SebastianOberschwendtner/OTP22_oScale/01_Code/src/gui.c

/**
 * OTP-22 oScale Firmware
 * Copyright (c) 2020 Sebastian Oberschwendtner, sebastian.oberschwendtner@gmail.com
 *
 *
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
 */
/**
 ******************************************************************************
 * @file    gui.c
 * @author  SO
 * @version V1.0.0
 * @date    22-November-2020
 * @brief   The GUI of the oScale.
 ******************************************************************************
 */
// ****** Includes ******
#include "gui.h"

// ****** Variables ******
task_t taskGUI; // Task struct for GUI
char buffer1[16]; // Buffer1 for display string
char buffer2[16]; // Buffer2 for display string
/*
 => double buffering is used, because the GUI does not know when the display is finished
 sending the data. Otherwise the GUI would override the content of the buffer while it
 is sent.
 */
ScaleDat_t* datGUI;  // Pointer to the system data.

// ****** Functions ******

/**
 **********************************************************
 * @brief TASK GUI
 **********************************************************
 * The GUI task.
 * 
 **********************************************************
 * @details
 * @Execution:	Non-interruptable
 **********************************************************
 */
void Task_GUI(void)
{
    // Switch for active command
    switch (taskGUI.command)
    {
    case GUI_CMD_INIT:
        gui_Init();
        break;

    case GUI_CMD_MANUAL:
        gui_DisplayManual();
        break;

    default:
        break;
    }
};

/**
 * @brief Initialize the GUI Data.
 */
void gui_InitTask(void)
{
    sarb_InitStruct(&taskGUI);
    taskGUI.command = GUI_CMD_INIT;

    // Get the pointer to the system data
    datGUI = Scale_GetIPC();
};

/**
 * @brief Initialize the GUI interface.
 */
void gui_Init(void)
{
    // Perform the command sequences
    switch (taskGUI.sequence)
    {
        case 0:
            // Write the header line
            if (gui_WriteString(0, 0, strcpy(buffer1, "oScale")))
                taskGUI.sequence++;
            break;

        case 1:
            // Write version to the header line
            if (gui_WriteString(8, 0, strcpy(buffer2, VERSION)))
                taskGUI.sequence++;
            break;

        case 2:
            // Write the horizontal line
            if (disp_CallByValue(DISP_CMD_LINE_H, 0, 128, 8))
                taskGUI.sequence++;
            break;

        case 3:
            taskGUI.counter = 0;
            // Write the vertical line
            if (disp_CallByValue(DISP_CMD_LINE_V, 1, 7, 64))
                taskGUI.sequence++;
            break;

        case 4:
            // Write the weight descriptor
            if (gui_WriteString(0, 2, strcpy(buffer1, "Weight")))
                taskGUI.sequence++;
            break;

        case 5:
            // Write the Time descriptor
            if (gui_WriteString(11, 2, strcpy(buffer2, "Time")))
                taskGUI.sequence++;
            break;

        case 6:
            // Write the weight units
            if (gui_WriteString(0, GUI_LINE_UNITS, strcpy(buffer1, "[g]")))
                taskGUI.sequence++;
            break;

        case 7:
            // Write the weight units
            if (gui_WriteString(11, GUI_LINE_UNITS, strcpy(buffer2, "[min]  [s]")))
                taskGUI.sequence++;
            break;

        case 8:
            // Command ist finished
            sarb_return(&taskGUI);
            taskGUI.command = GUI_CMD_MANUAL;
            break;

        default:
            break;
    }
};

/**
 * @brief Perform the normal GUI operation.
 */
void gui_DisplayManual(void)
{
    // Perform the command sequence
    switch (taskGUI.sequence)
    {
    case 0:
        // Display the measured weight
        if (gui_WriteWeight())
            taskGUI.sequence++;
        break;

    case 1:
        // Display the passed time
        if(gui_WriteTime())
            taskGUI.sequence++;
        break;

    case 2:
        // Display the passed time
        if(gui_WriteBattery())
            sarb_return(&taskGUI);
        break;

    default:
        break;
    }
};

/**
 * @brief Write a string at at specified cursor position to the display.
 * @param x The x-position for the string.
 * @param line The line number for the string.
 * @param buffer The pointer to the string buffer.
 * @return Returns 1 when the string write was successfully triggered.
 */
unsigned char gui_WriteString(unsigned char x, unsigned char line, char *buffer)
{
    // Only when display is not busy
    if (!disp_IsBusy())
    {
        // set the cursor
        disp_SetCursorX(x);
        disp_SetLine(line);

        // Write the string until the end is reached
        return disp_CallByReference(DISP_CMD_WRITE_STRING, buffer);
    }
    return 0;
};

/**
 * @brief Display the current measured weight in the display.
 * @return Returns 1 when the data write was successfully triggered.
 */
unsigned char gui_WriteWeight(void)
{
    unsigned int _weight = 0;
    unsigned int _digit = 0;

    // Only when weight is positive
    if (datGUI->Weight > 0)
        _weight = (unsigned int)datGUI->Weight;

    //When display is not busy
    if (!disp_IsBusy())
    {
        // Get the single digits to display
        // Digit 0
        _digit = _weight / 1000;
        _weight -= 1000 * _digit;
        buffer1[0] = (unsigned char)(_digit + 48);
        // Digit 1
        _digit = _weight / 100;
        _weight -= 100 * _digit;
        buffer1[1] = (unsigned char)(_digit + 48);
        // Digit 2
        _digit = _weight / 10;
        _weight -= 10 * _digit;
        buffer1[2] = (unsigned char)(_digit + 48);
        buffer1[3] = '.';
        // Digit 3
        buffer1[4] = (unsigned char)(_weight + 48);
        buffer1[5] = 0;

        // Set cursor
        disp_SetCursorX(1);
        disp_SetLine(GUI_LINE_VALUES);

        // Write the content
        return disp_CallByReference(DISP_CMD_WRITE_NUMBER, buffer1);
    }
    return 0;
};

/**
 * @brief Display the passed time in the display.
 * @return Returns 1 when the data write was successfully triggered.
 */
unsigned char gui_WriteTime(void)
{
    unsigned int _time = datGUI->Time;
    unsigned int _digit = 0;
    //When display is not busy
    if (!disp_IsBusy())
    {
        // Get the single digits to display
        // Digit 0
        _digit = _time / 600;
        _time -= 600 * _digit;
        buffer2[0] = (unsigned char)(_digit + 48);
        // Digit 1
        _digit = _time / 60;
        _time -= 60 * _digit;
        buffer2[1] = (unsigned char)(_digit + 48);
        buffer2[2] = ':';
        // Digit 2
        _digit = _time / 10;
        _time -= 10 * _digit;
        buffer2[3] = (unsigned char)(_digit + 48);
        
        // Digit 3
        buffer2[4] = (unsigned char)(_time + 48);
        buffer2[5] = 0;

        // Set cursor
        disp_SetCursorX(12);
        disp_SetLine(GUI_LINE_VALUES);

        // Write the content
        return disp_CallByReference(DISP_CMD_WRITE_NUMBER, buffer2);
    }
    return 0;
};

/**
 * @brief Display the charge of the battery.
 * @return Returns 1 when the data write was successfully triggered.
 */
unsigned char gui_WriteBattery(void)
{
    //When display is not busy
    if (!disp_IsBusy())
    {
        // Set cursor
        disp_SetCursorX(16);
        disp_SetLine(0);

        // Get the SoC
        GUI_Num2Str(buffer1, datGUI->SoC, 2);
        buffer1[2] = '%';
        buffer1[3] = ' ';
        buffer1[4] = 7 + (datGUI->SoC/25);
        buffer1[5] = 0;


        // Write the content
        return disp_CallByReference(DISP_CMD_WRITE_STRING, buffer1);
    }
    return 0;
};

/**
 * @brief Trigger the GUI task to write the screen.
 * @param screen The type of screen to display.
 * @return Returns 1 when screen write was successfully triggered.
 */
unsigned char GUI_Draw(unsigned char screen)
{
    //Only call command when no other command is active
    if (taskGUI.command == 0)
    {
        // Set the commands data
        taskGUI.argument[0] = 0;
        taskGUI.argument[1] = 0;
        taskGUI.argument[2] = 0;
        taskGUI.command     = screen;
        taskGUI.sequence    = 0;
        return 1;
    }
    return 0;
};

/**
 * @brief Save the specified integer as a number string to a string buffer.
 * The destination buffer has to be long enough to contain the digits!
 * @param dest Pointer to the destination buffer.
 * @param int_number The integer number to convert.
 * @param precision The number of digits to convert.
 * @return Returns the pointer address of the modified destination string.
 */
char* GUI_Num2Str(char* dest, unsigned int int_number, unsigned char precision)
{
    // Temporary variables
    unsigned int i_buffer = int_number;
    unsigned char ch_digit = 0;
    
    // Repeat for every digit
    for (unsigned char digit = precision; digit > 0; digit--)
    {
        // Get the current digit
        ch_digit = i_buffer % 10;
        i_buffer /= 10;

        // Save the digit to the buffer
        *(dest+(digit-1)) = ch_digit + 48;
    }

    // Terminate and return the string
    *(dest + precision) = 0;
    return dest;
};
